PhilKes/LEDSpielAnzeige/doc/eagle/LEDAnzeige_Multiplexing_Board_mirror.png

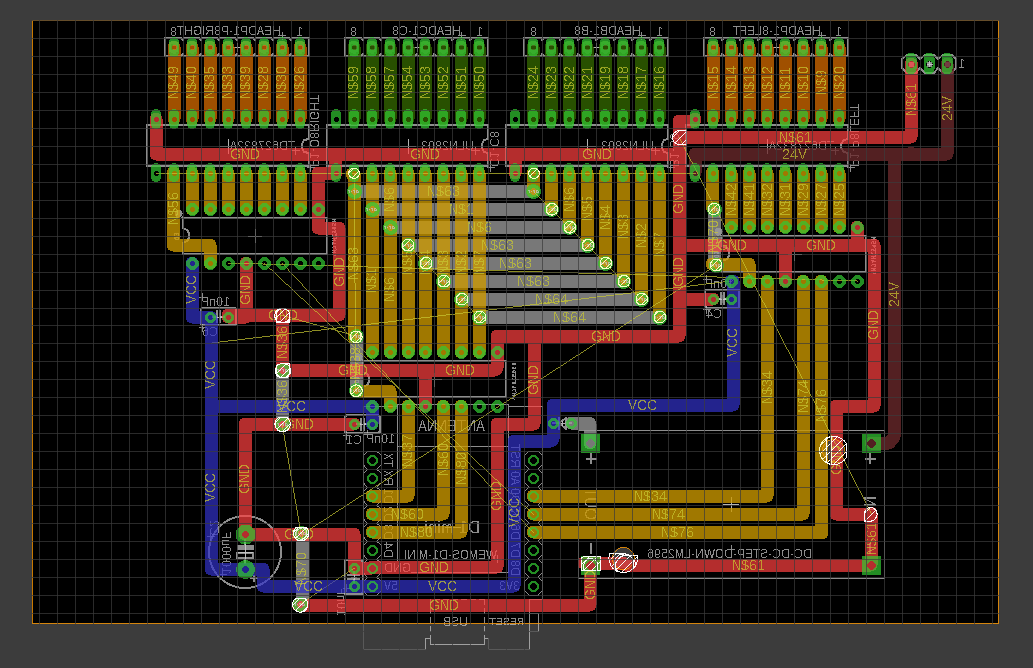
doc/eagle/LEDAnzeige_Multiplexing_Board_mirror.png
