PhilKes/LEDSpielAnzeige/wemos/wemos_platformio_react/src/LightStateService.cpp

#include <LightStateService.h>

LightStateService::LightStateService(AsyncWebServer* server,
                                     SecurityManager* securityManager
                                    ) :
    _httpEndpoint(LightState::read,
                  LightState::update,
                  this,
                  server,
                  LIGHT_SETTINGS_ENDPOINT_PATH,
                  securityManager,
                  AuthenticationPredicates::IS_AUTHENTICATED),
    _webSocket(LightState::read,
               LightState::update,
               this,
               server,
               LIGHT_SETTINGS_SOCKET_PATH,
               securityManager,
               AuthenticationPredicates::IS_AUTHENTICATED){

  // configure settings service update handler to update LED state
  addUpdateHandler([&](const String& originId) { onConfigUpdated(); }, false);
}

void LightStateService::begin() {
  _state.ledOn = DEFAULT_LED_STATE;
  onConfigUpdated();
}

void LightStateService::onConfigUpdated() {
  digitalWrite(BLINK_LED, _state.ledOn ? LED_ON : LED_OFF);
}

void LightStateService::registerConfig() {

  String configTopic;
  String subTopic;
  String pubTopic;

  DynamicJsonDocument doc(256);

  doc["cmd_t"] = "~/set";
  doc["stat_t"] = "~/state";
  doc["schema"] = "json";
  doc["brightness"] = false;

  String payload;
  serializeJson(doc, payload);

}
